MATTMCCA/FragNinja/Frag-Ninja_001/Pics/bl-flash.jpeg

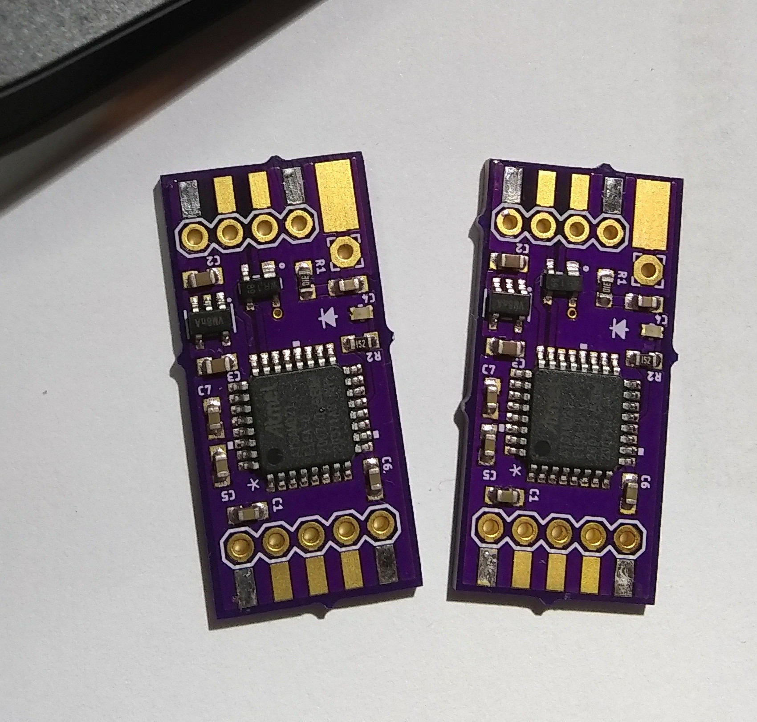
Frag-Ninja_001/Pics/bl-flash.jpeg
