MATTMCCA/FragNinja/Frag-Ninja_001/Pics/Board_Check/first_run.jpeg

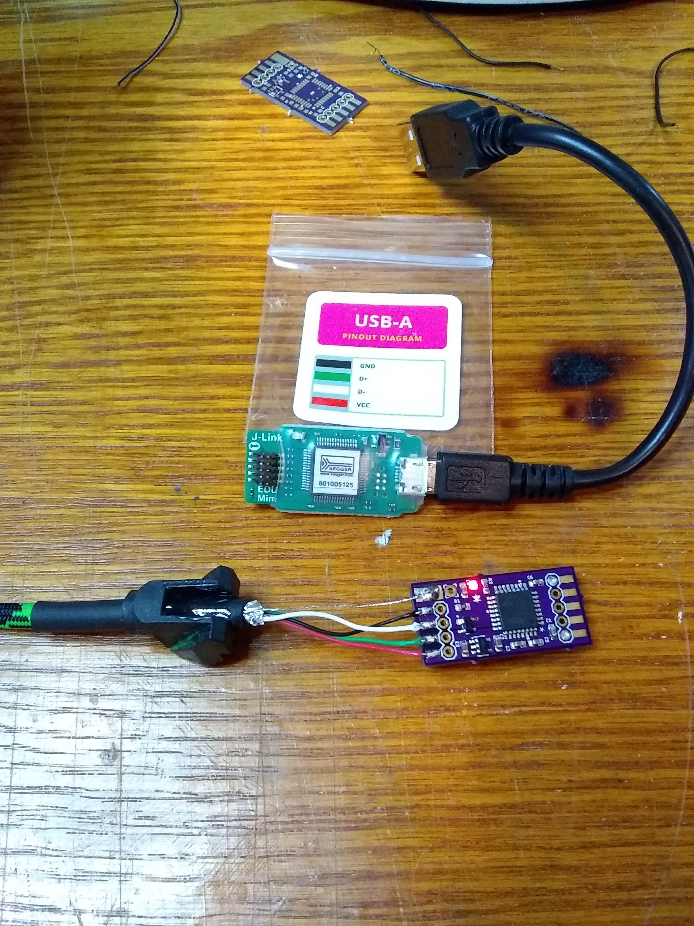
Frag-Ninja_001/Pics/Board_Check/first_run.jpeg
