MATTMCCA/FragNinja/Frag-Ninja_001/Pics/Board_Check/size_check_003.jpg

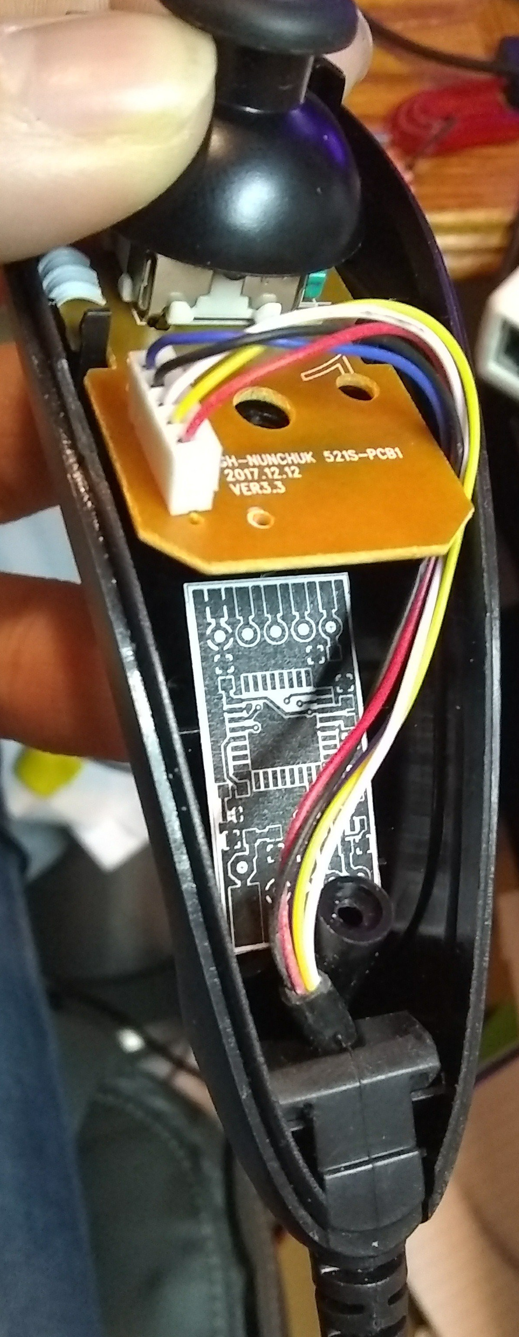
Frag-Ninja_001/Pics/Board_Check/size_check_003.jpg
