MATTMCCA/FragNinja/Frag-Ninja_001/Pics/BRD_FULL.png

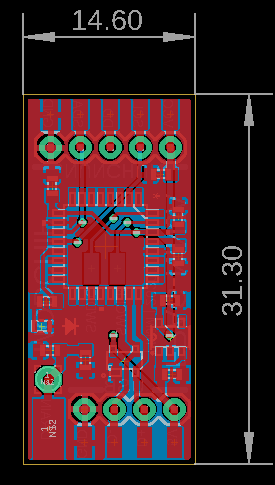
Frag-Ninja_001/Pics/BRD_FULL.png
