MATTMCCA/FragNinja/Frag-Ninja_001/Pics/cable/cable_1.jpg

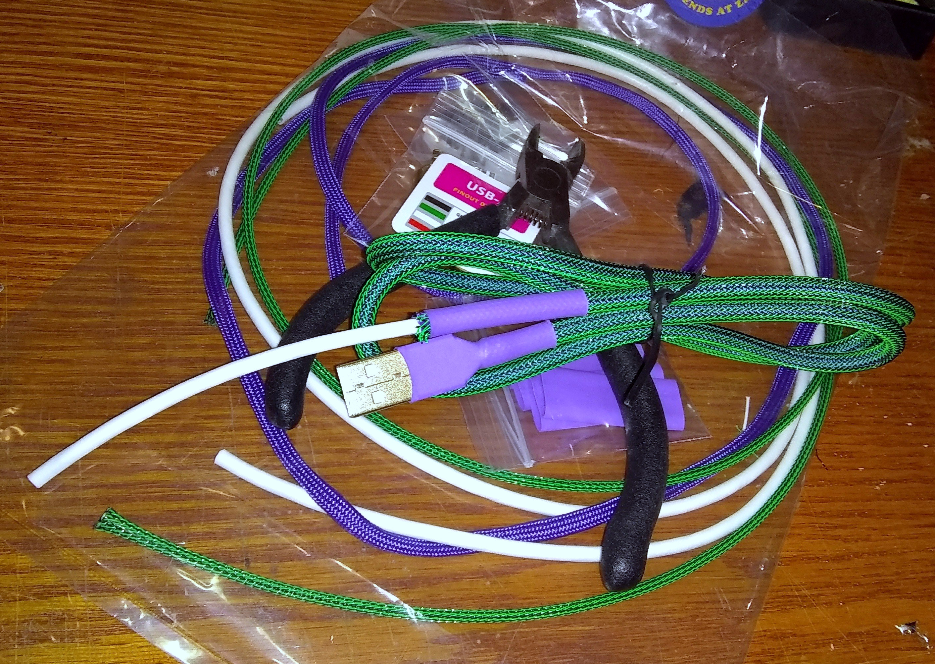
Frag-Ninja_001/Pics/cable/cable_1.jpg
