MATTMCCA/FragNinja/Frag-Ninja_001/Pics/oshpark_front.png

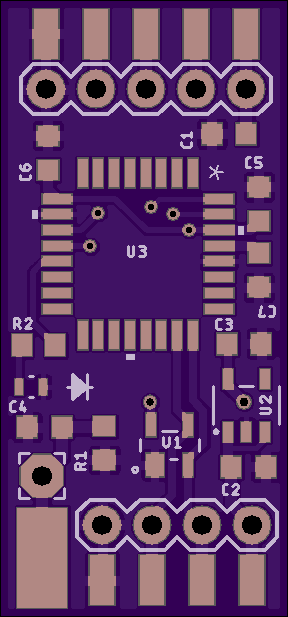
Frag-Ninja_001/Pics/oshpark_front.png
